jabiluengo/noise/photos/IMG_20200701_112004.jpg

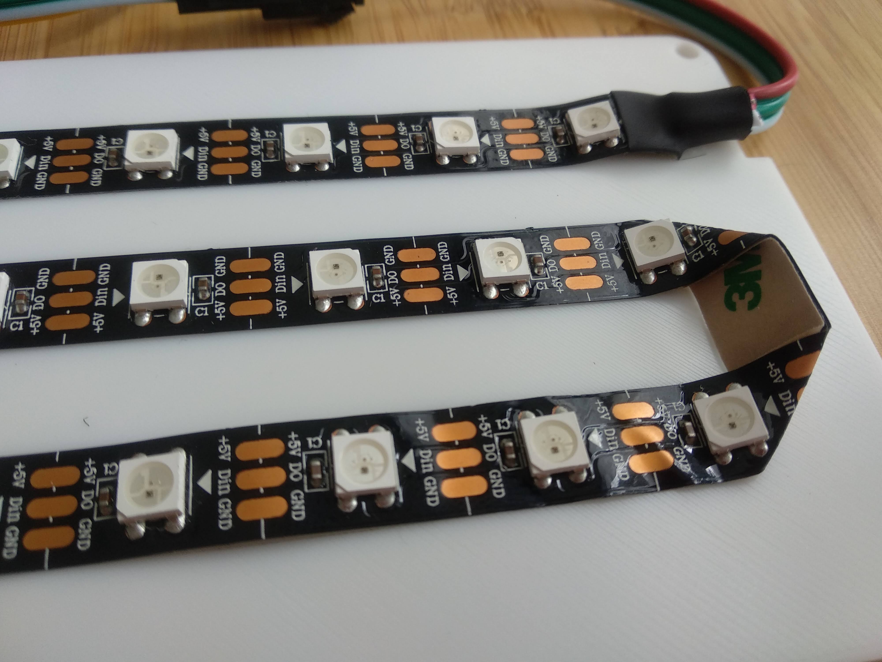
photos/IMG_20200701_112004.jpg
