jabiluengo/noise/photos/IMG_20200701_112025.jpg

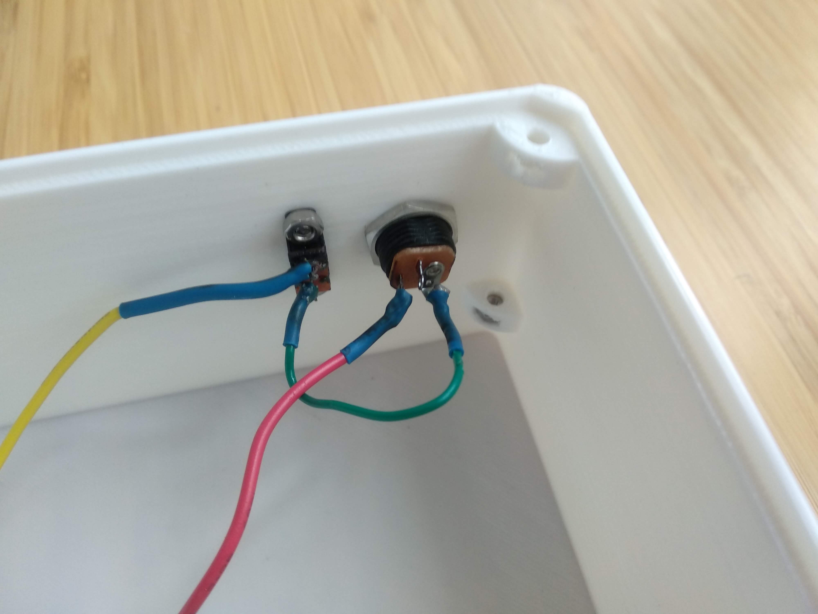
photos/IMG_20200701_112025.jpg
