jabiluengo/noise/photos/IMG_20200701_112042.jpg

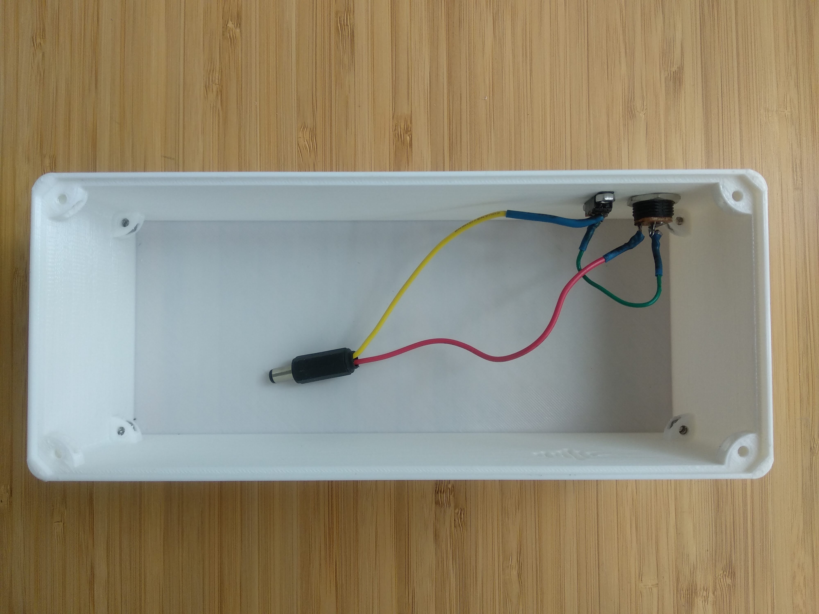
photos/IMG_20200701_112042.jpg
