jabiluengo/noise/photos/IMG_20200701_112142.jpg

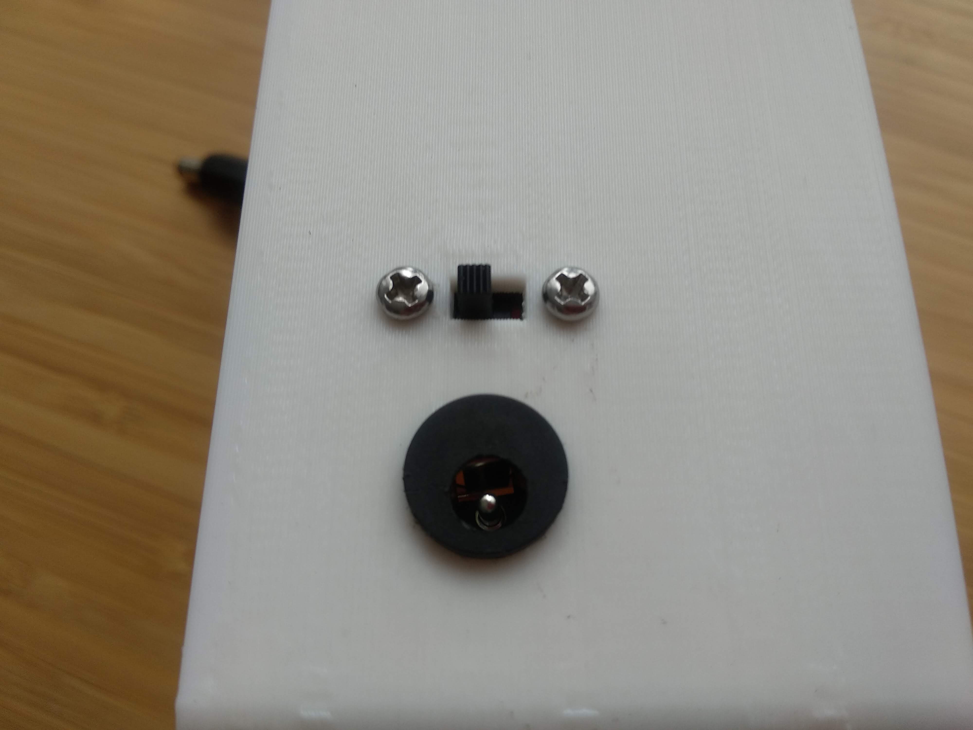
photos/IMG_20200701_112142.jpg
