jabiluengo/noise/photos/IMG_20200701_112244.jpg

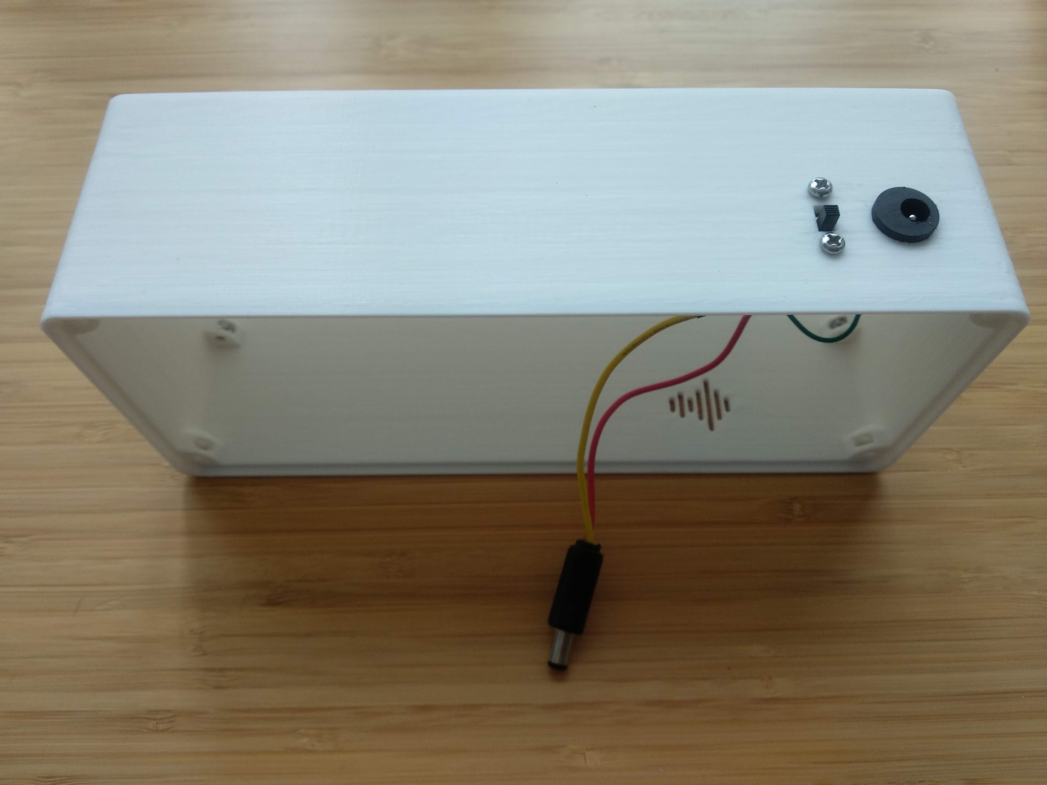
photos/IMG_20200701_112244.jpg
