jabiluengo/noise/photos/IMG_20200701_132034.jpg

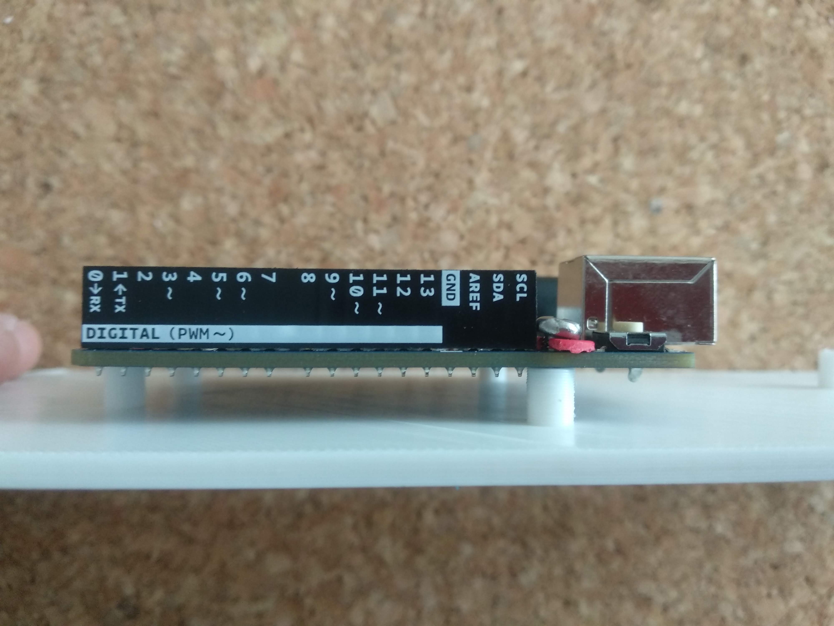
photos/IMG_20200701_132034.jpg
