jabiluengo/noise/photos/IMG_20200701_132056.jpg

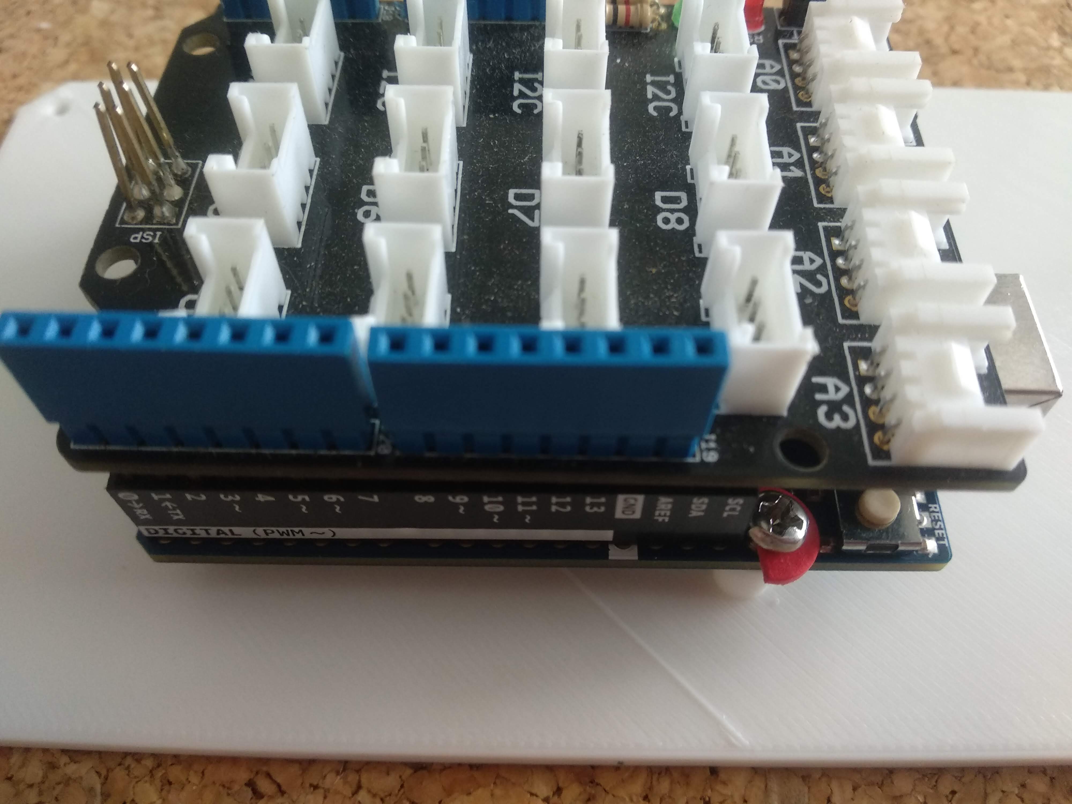
photos/IMG_20200701_132056.jpg
