jabiluengo/noise/photos/IMG_20200701_132346.jpg

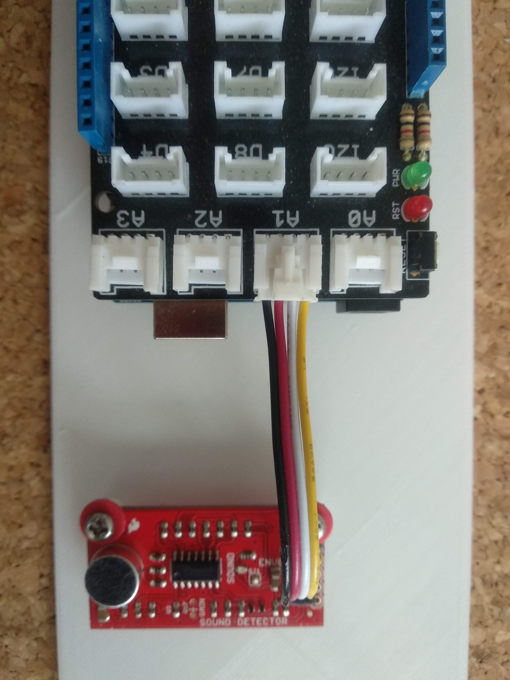
photos/IMG_20200701_132346.jpg
