jabiluengo/noise/photos/IMG_20200701_133257.jpg

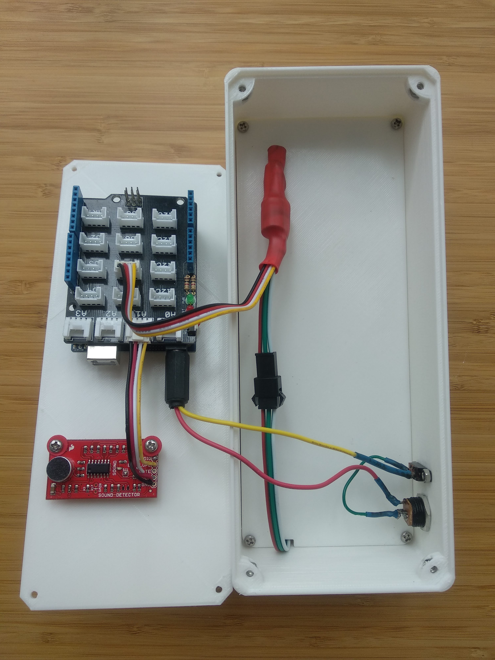
photos/IMG_20200701_133257.jpg
